AMCC1998/Robo-de-Luta/01.ficheiros_3d/Botzilla_braco_servo.stl

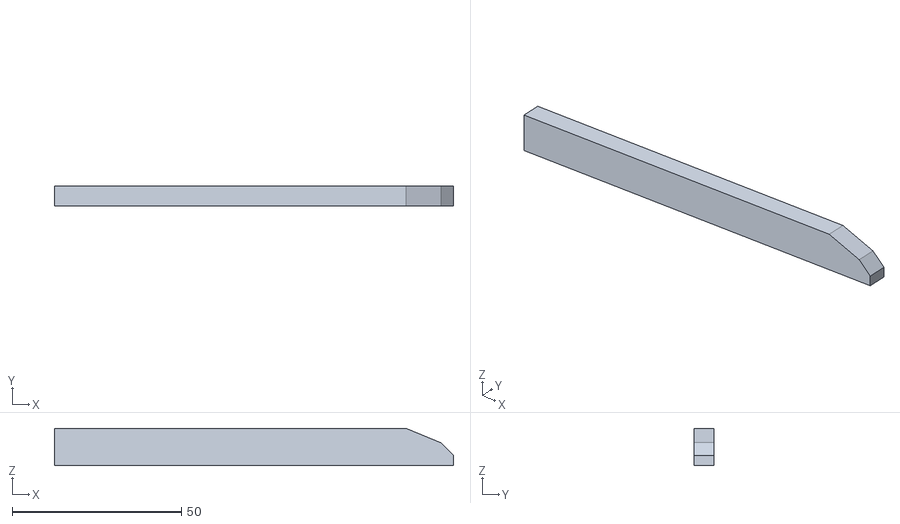
[picture p15: CAD file, 2025-08-01]
01.ficheiros_3d/Botzilla_braco_servo.stl
118.0 x 6.00 x 11.0
