AMCC1998/Robo-de-Luta/01.ficheiros_3d/v2/Botzilla_frame_esquerda.stl

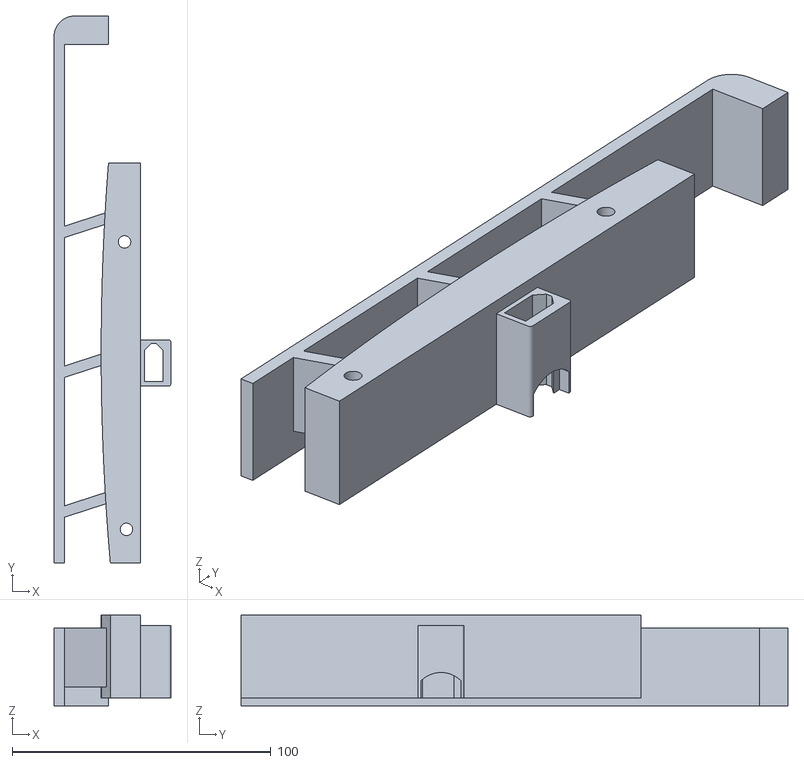
[picture p17: CAD file, 2025-10-28]
01.ficheiros_3d/v2/Botzilla_frame_esquerda.stl
45.2 x 211.2 x 35.0
