AMCC1998/Robo-de-Luta/01.ficheiros_3d/suporte_arma_esq.stl

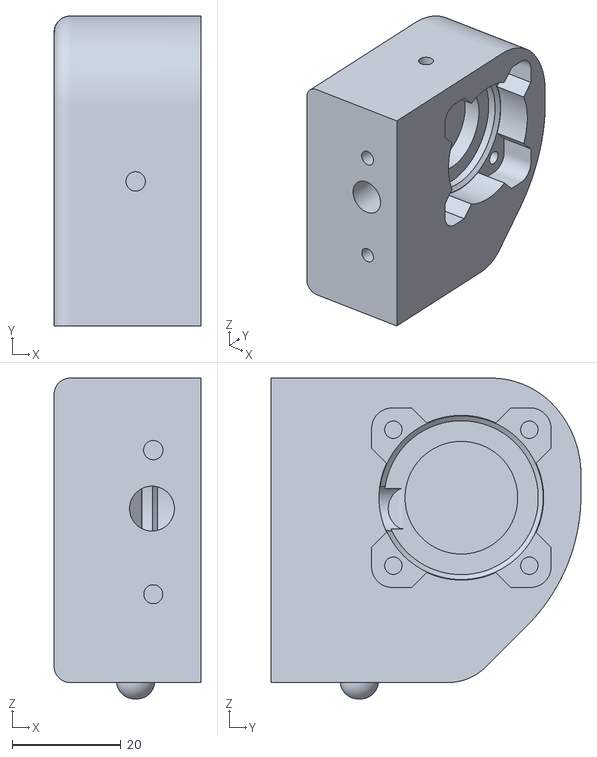
[picture p18: CAD file, 2025-08-01]
01.ficheiros_3d/suporte_arma_esq.stl
27.0 x 57.0 x 59.0
