AMCC1998/Robo-de-Luta/01.ficheiros_3d/v2/Suporte_fuzivel_2.stl

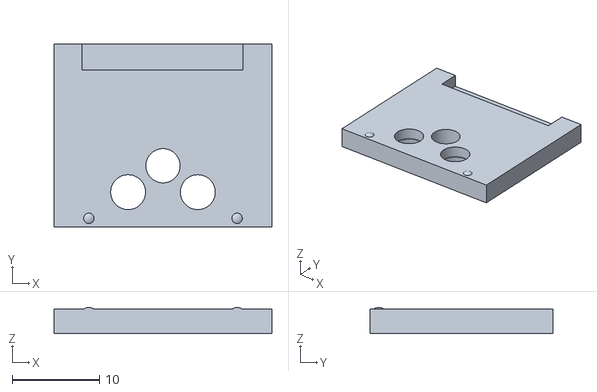
[picture p19: CAD file, 2025-10-28]
01.ficheiros_3d/v2/Suporte_fuzivel_2.stl
25.0 x 21.0 x 3.00
