AMCC1998/Robo-de-Luta/01.ficheiros_3d/body_tras.stl

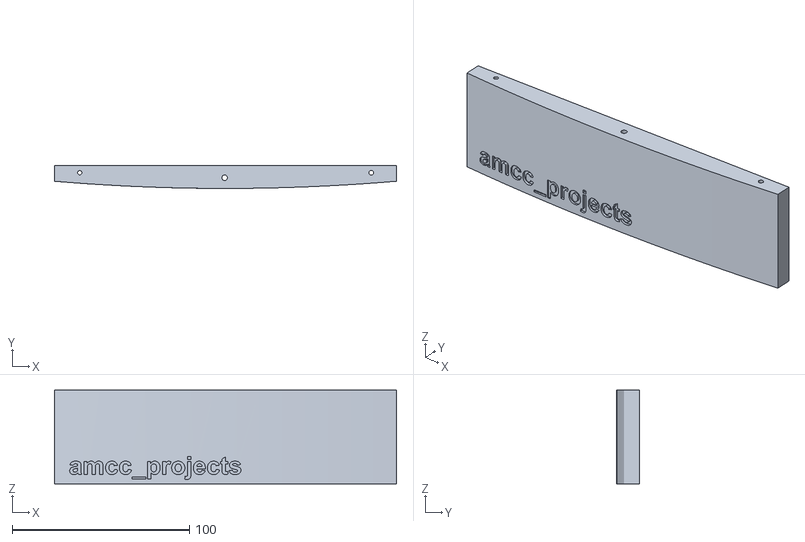
[picture p20: CAD file, 2025-08-01]
01.ficheiros_3d/body_tras.stl
193.0 x 12.9 x 53.0
