AMCC1998/Robo-de-Luta/01.ficheiros_3d/v2/Arma_4.stl

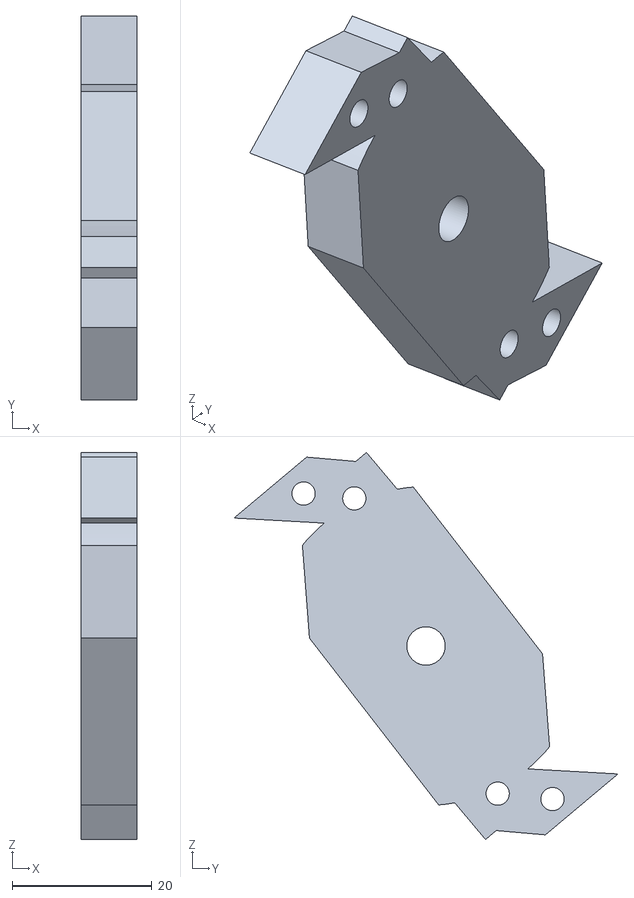
[picture p21: CAD file, 2025-10-28]
01.ficheiros_3d/v2/Arma_4.stl
8.00 x 55.0 x 55.5
