AMCC1998/Robo-de-Luta/01.ficheiros_3d/Tampa_superior_1mm.stl

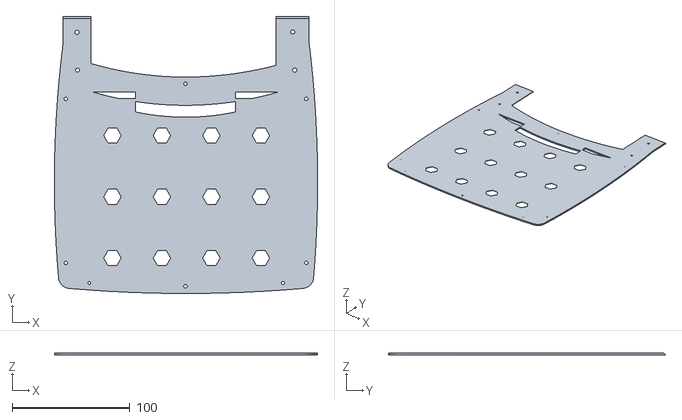
[picture p22: CAD file, 2025-08-01]
01.ficheiros_3d/Tampa_superior_1mm.stl
223.4 x 235.1 x 1.50
