AMCC1998/Robo-de-Luta/01.ficheiros_3d/Botzilla_lateral_esq.stl

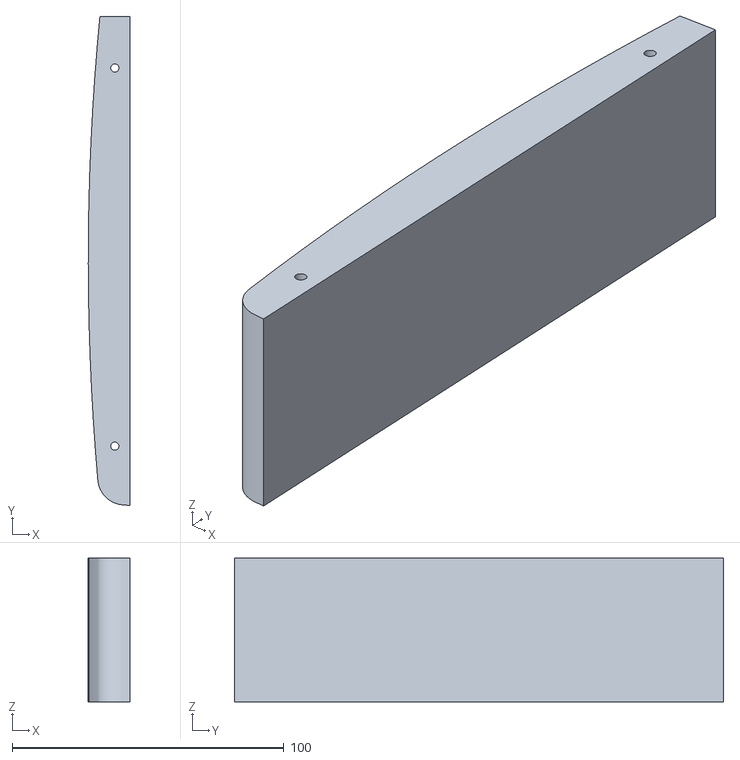
[picture p23: CAD file, 2025-08-01]
01.ficheiros_3d/Botzilla_lateral_esq.stl
15.3 x 180.0 x 53.0
