AMCC1998/Robo-de-Luta/01.ficheiros_3d/v2/Botzilla_frame_tras.stl

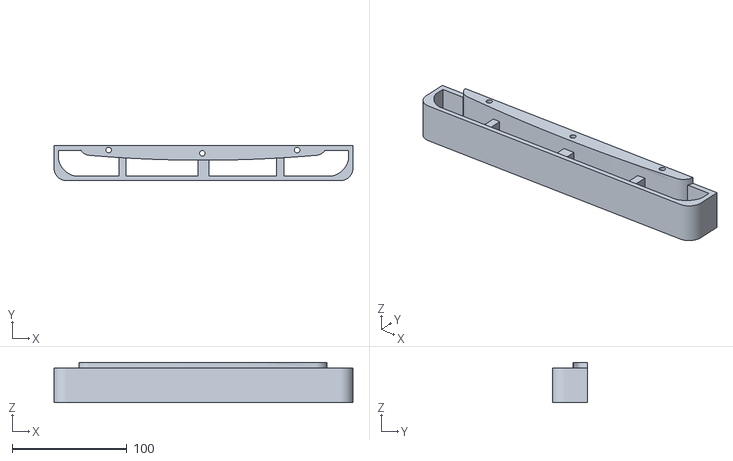
[picture p24: CAD file, 2025-10-28]
01.ficheiros_3d/v2/Botzilla_frame_tras.stl
261.0 x 30.8 x 35.0
