AMCC1998/Robo-de-Luta/01.ficheiros_3d/v2/Roda.stl

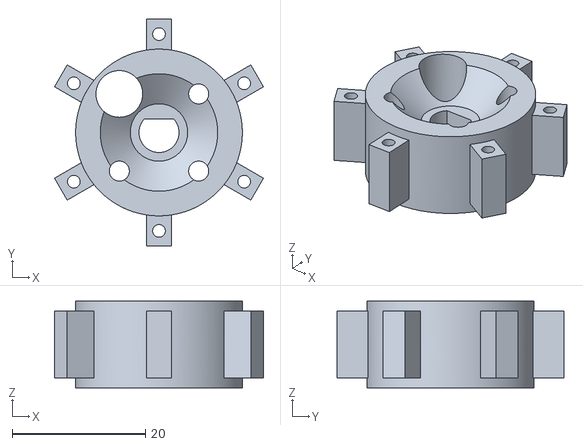
[picture p26: CAD file, 2025-10-28]
01.ficheiros_3d/v2/Roda.stl
31.3 x 34.0 x 13.0
