AMCC1998/Robo-de-Luta/01.ficheiros_3d/cabo_ferramenta_bloqueio.stl

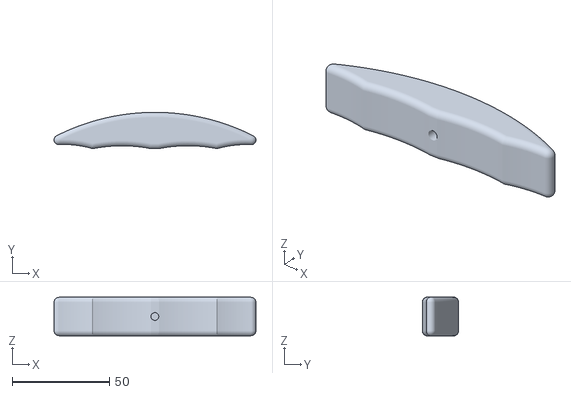
[picture p27: CAD file, 2025-08-01]
01.ficheiros_3d/cabo_ferramenta_bloqueio.stl
103.9 x 18.7 x 20.0
