AMCC1998/Robo-de-Luta/01.ficheiros_3d/v2/Arma.step

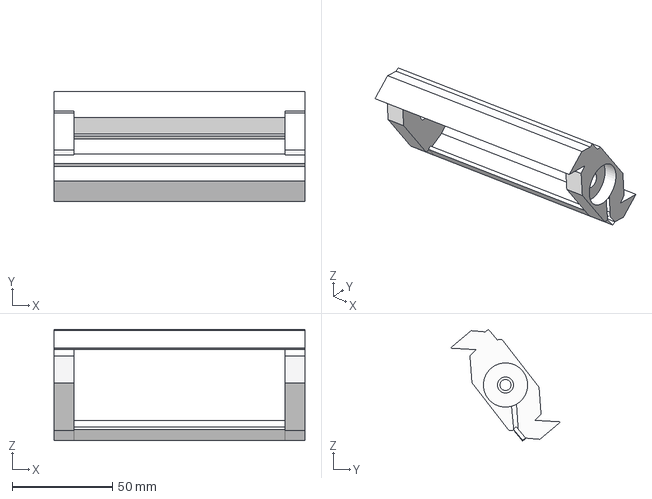
[picture p28: CAD file, 2025-10-28]
01.ficheiros_3d/v2/Arma.step
125.0 x 55.0 x 55.5 mm
