AMCC1998/Robo-de-Luta/01.ficheiros_3d/v2/Arma_dir.stl

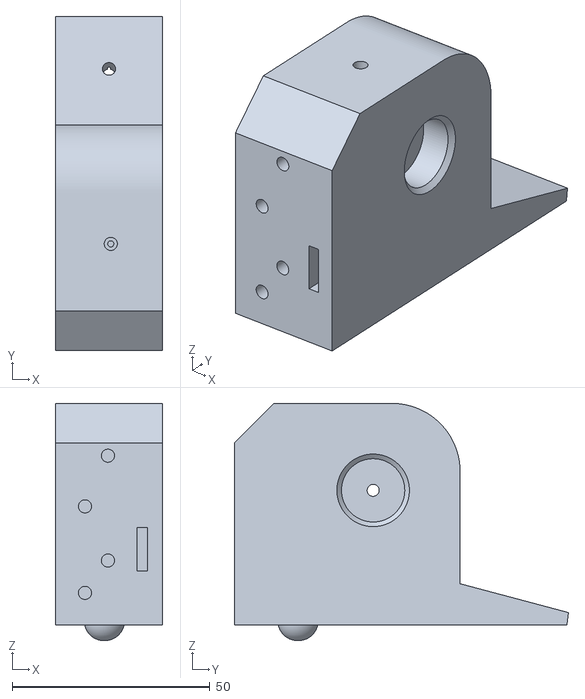
[picture p29: CAD file, 2025-10-28]
01.ficheiros_3d/v2/Arma_dir.stl
27.1 x 84.5 x 60.0
