AMCC1998/Robo-de-Luta/01.ficheiros_3d/base_baixo.stl

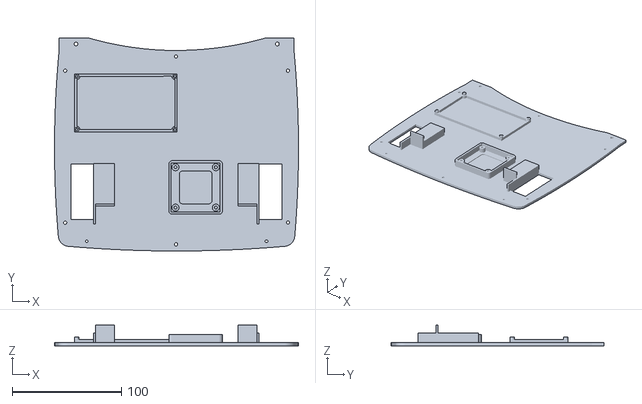
[picture p30: CAD file, 2025-08-01]
01.ficheiros_3d/base_baixo.stl
223.4 x 195.1 x 19.0
