AMCC1998/Robo-de-Luta/01.ficheiros_3d/v2/Molde_pneu.stl

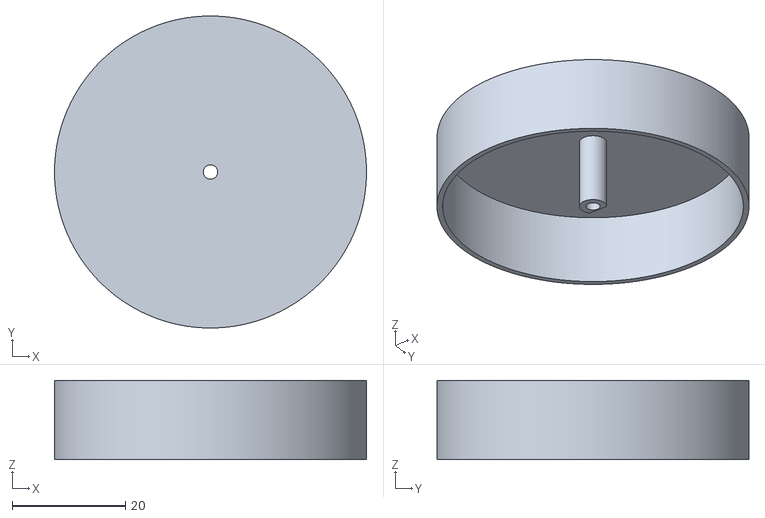
[picture p31: CAD file, 2025-10-28]
01.ficheiros_3d/v2/Molde_pneu.stl
55.0 x 55.0 x 14.0
