AMCC1998/Robo-de-Luta/01.ficheiros_3d/body_frente.stl

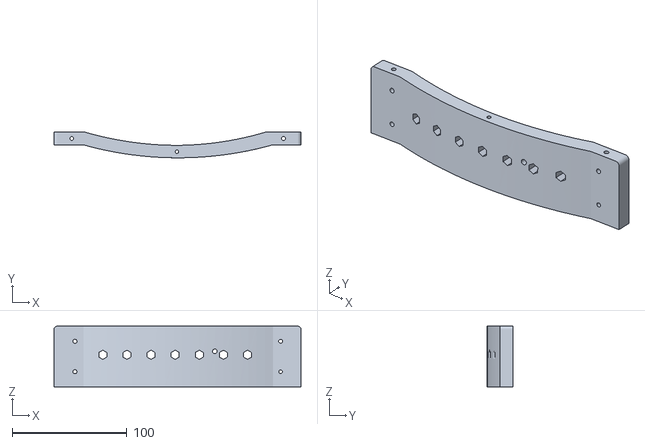
[picture p32: CAD file, 2025-08-01]
01.ficheiros_3d/body_frente.stl
215.0 x 22.3 x 53.0
