AMCC1998/Robo-de-Luta/01.ficheiros_3d/v2/Botzilla_frame_direita.stl

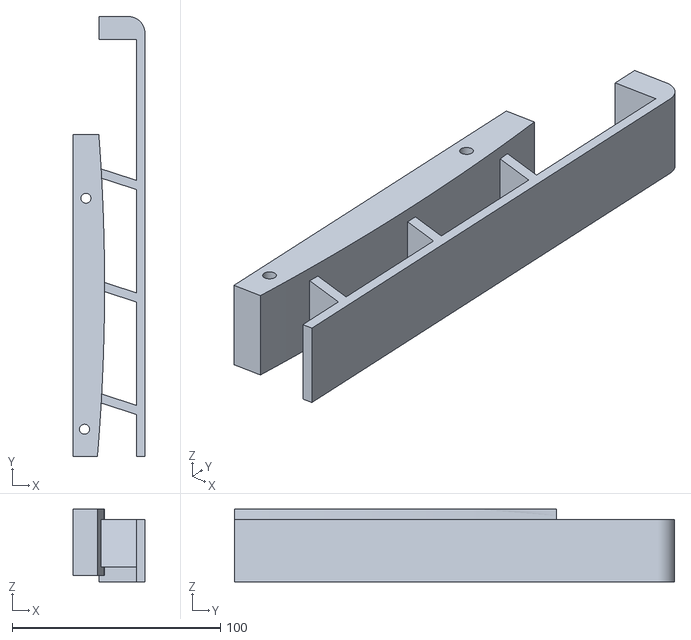
[picture p33: CAD file, 2025-10-28]
01.ficheiros_3d/v2/Botzilla_frame_direita.stl
34.5 x 211.2 x 35.0
