AMCC1998/Robo-de-Luta/01.ficheiros_3d/suporte_motor.stl

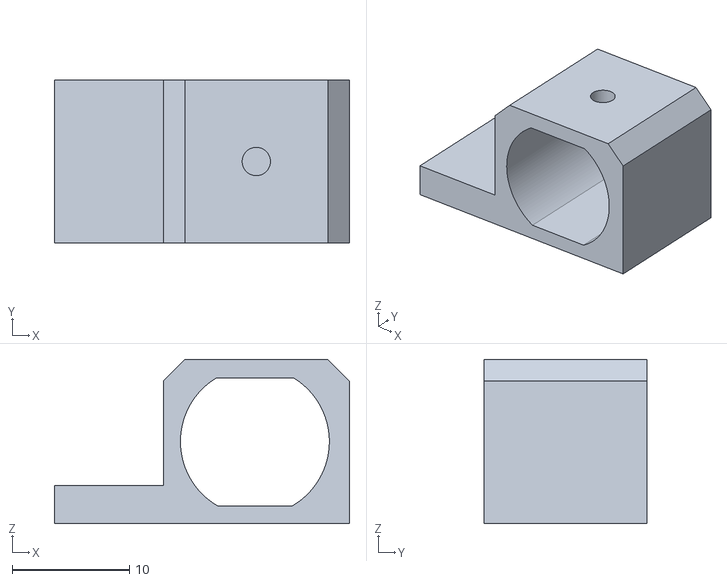
[picture p34: CAD file, 2025-06-23]
01.ficheiros_3d/suporte_motor.stl
25.1 x 13.9 x 14.0
