AMCC1998/Robo-de-Luta/01.ficheiros_3d/molde_pneu_roda.stl

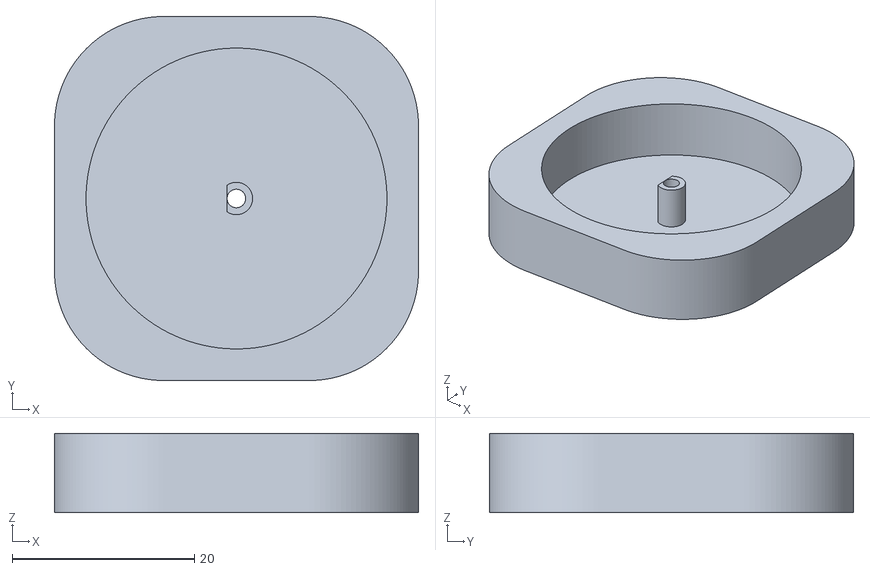
[picture p36: CAD file, 2025-06-23]
01.ficheiros_3d/molde_pneu_roda.stl
40.0 x 40.0 x 8.70
