AMCC1998/Robo-de-Luta/01.ficheiros_3d/v2/tampa_superior.stl

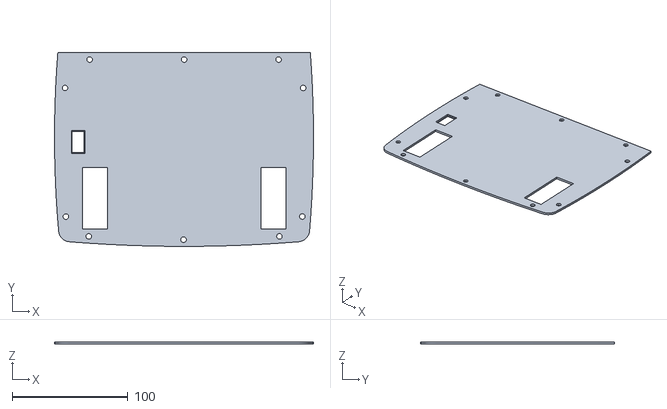
[picture p37: CAD file, 2025-10-28]
01.ficheiros_3d/v2/tampa_superior.stl
223.4 x 167.2 x 2.00
