AMCC1998/Robo-de-Luta/01.ficheiros_3d/molde_roda_Rodas.stl

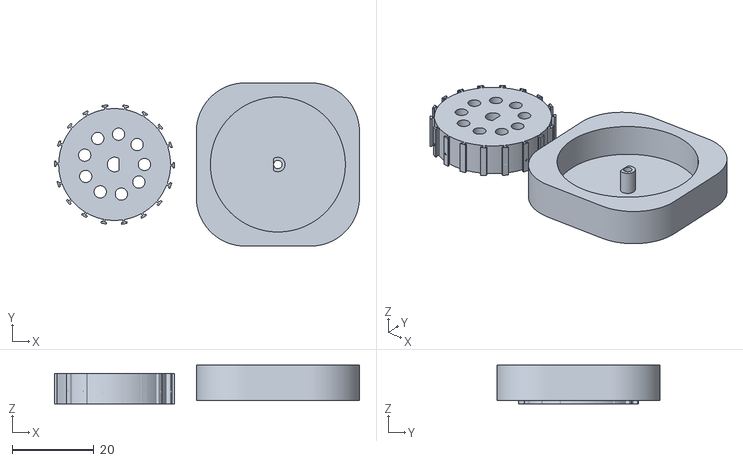
[picture p38: CAD file, 2025-06-23]
01.ficheiros_3d/molde_roda_Rodas.stl
74.7 x 40.0 x 9.50
