AMCC1998/Robo-de-Luta/01.ficheiros_3d/roda.stl

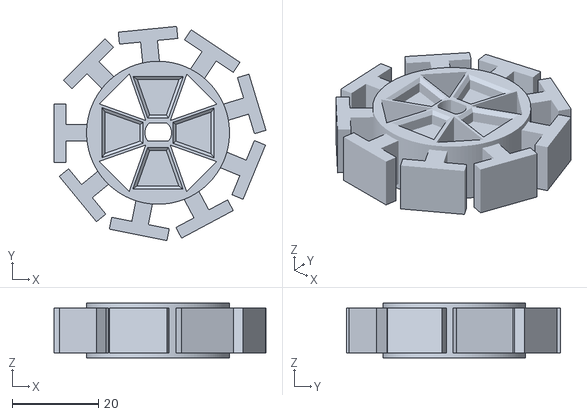
[picture p39: CAD file, 2025-06-23]
01.ficheiros_3d/roda.stl
49.2 x 49.7 x 12.7
