AMCC1998/Robo-de-Luta/01.ficheiros_3d/v2/Base_motor.stl

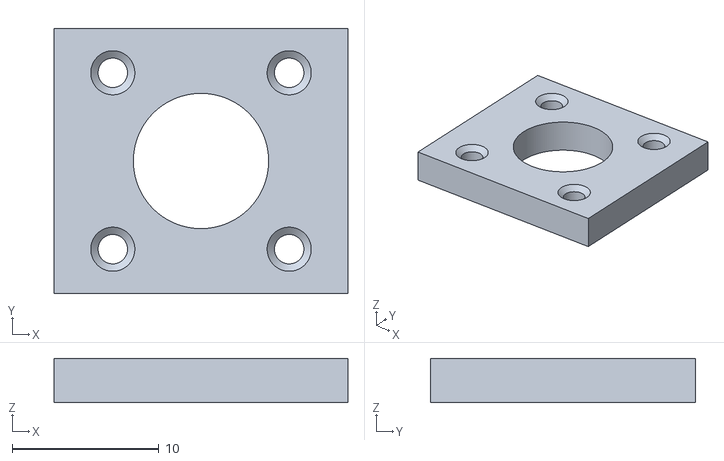
[picture p40: CAD file, 2025-09-01]
01.ficheiros_3d/v2/Base_motor.stl
20.0 x 18.0 x 3.00
