AMCC1998/Robo-de-Luta/01.ficheiros_3d/v2/Robo de luta v2.stl

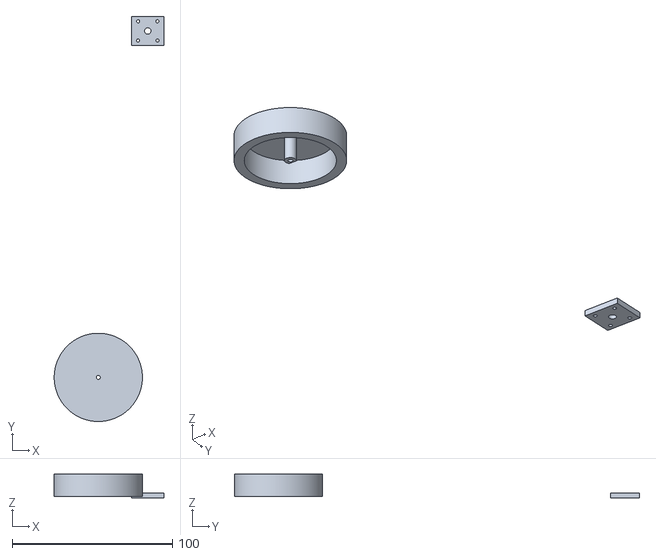
[picture p41: CAD file, 2025-09-01]
01.ficheiros_3d/v2/Robo de luta v2.stl
68.3 x 252.4 x 14.8
