AMCC1998/Robo-de-Luta/01.ficheiros_3d/v2/lateral_esq.stl

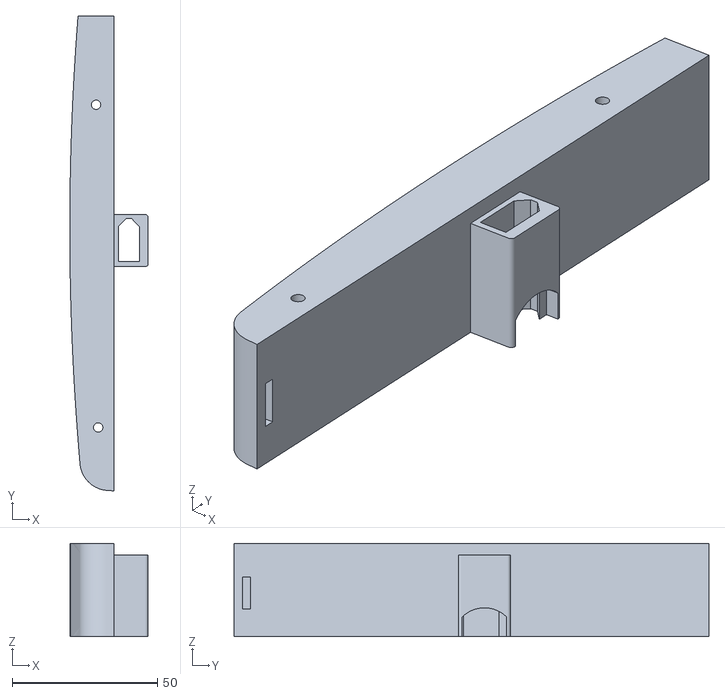
[picture p42: CAD file, 2025-09-01]
01.ficheiros_3d/v2/lateral_esq.stl
27.0 x 163.4 x 32.0
