AMCC1998/Robo-de-Luta/01.ficheiros_3d/v2/Body 51.stl

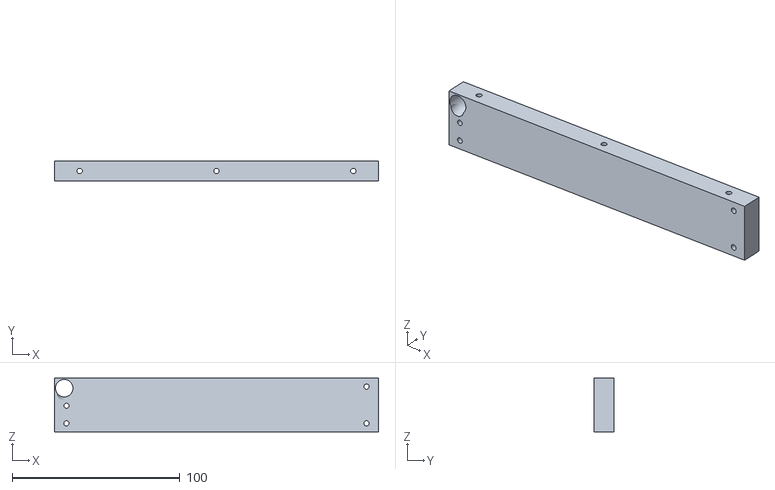
[picture p43: CAD file, 2025-09-01]
01.ficheiros_3d/v2/Body 51.stl
193.0 x 12.0 x 32.0
