AMCC1998/Robo-de-Luta/01.ficheiros_3d/v2/Botzilla.3mf

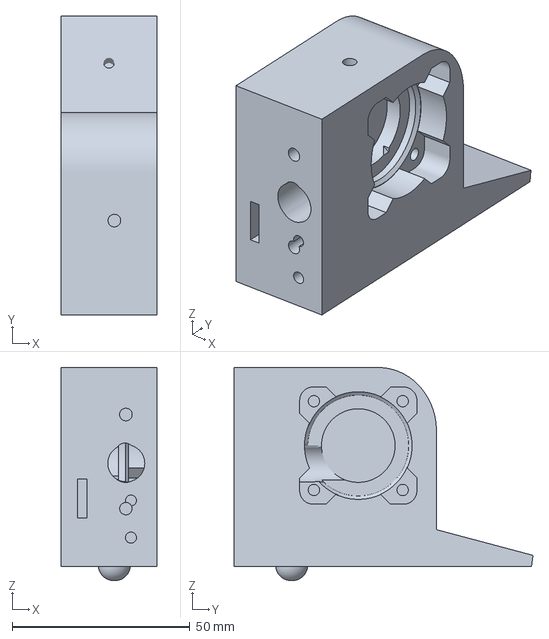
[picture p44: CAD file, 2025-09-01]
01.ficheiros_3d/v2/Botzilla.3mf
27.0 x 84.2 x 60.0 mm
