AMCC1998/Robo-de-Luta/01.ficheiros_3d/v2/Robo de luta v12.step

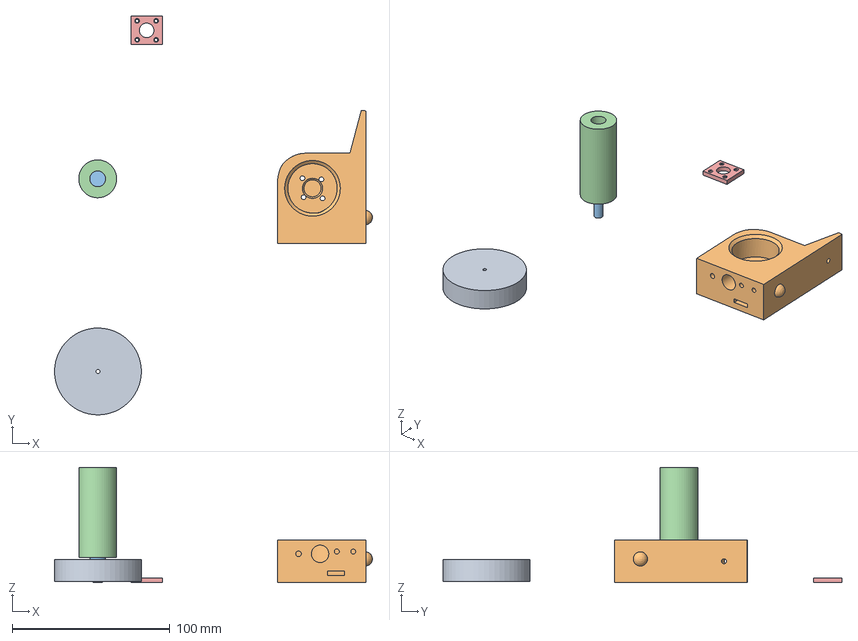
[picture p45: CAD file, 2025-09-01]
01.ficheiros_3d/v2/Robo de luta v12.step
201.3 x 252.4 x 73.0 mm
Molde_pneu
suporte arma esq
