AMCC1998/Robo-de-Luta/01.ficheiros_3d/v2/Body1.stl

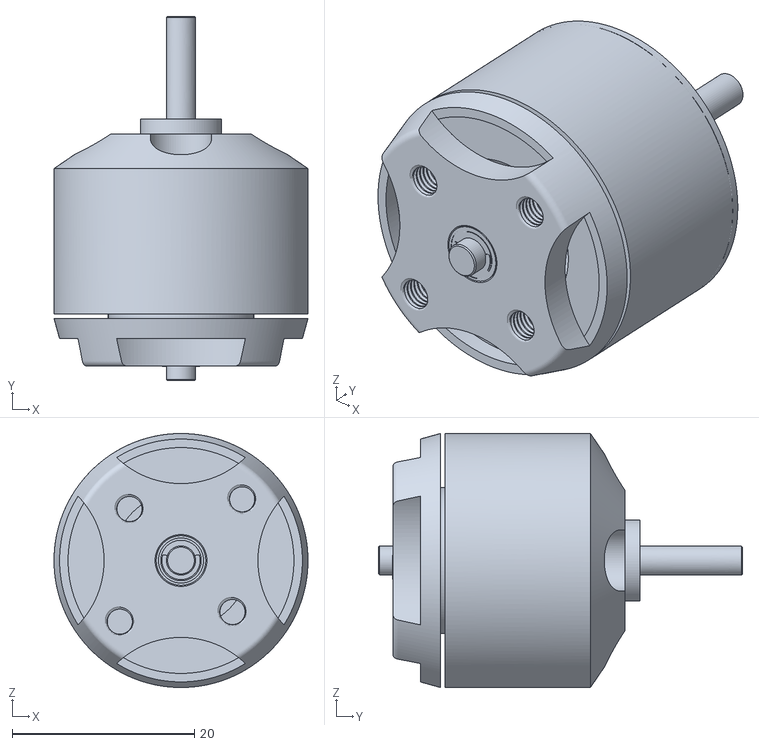
[picture p46: CAD file, 2025-09-01]
01.ficheiros_3d/v2/Body1.stl
27.9 x 40.0 x 27.9
