AMCC1998/Robo-de-Luta/01.ficheiros_3d/v2/Botzilla_lateral_traseira.stl

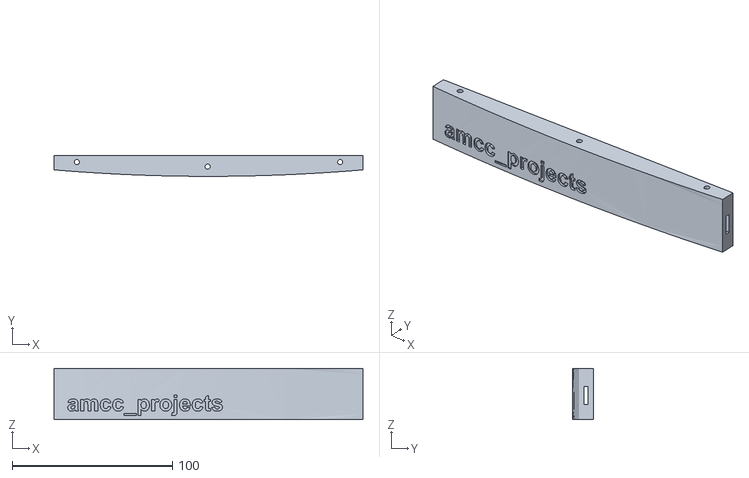
[picture p47: CAD file, 2025-09-01]
01.ficheiros_3d/v2/Botzilla_lateral_traseira.stl
193.0 x 12.9 x 32.0
