AMCC1998/Robo-de-Luta/01.ficheiros_3d/v2/suporte arma esq.step

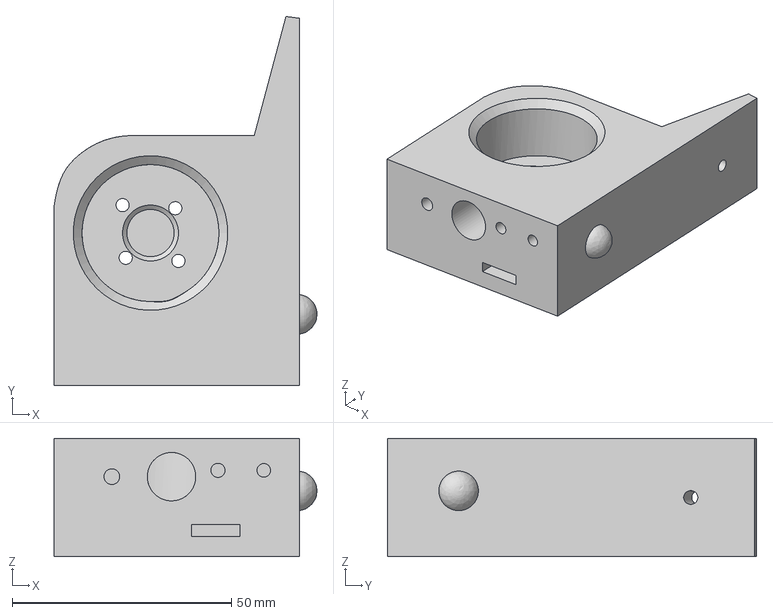
[picture p48: CAD file, 2025-09-01]
01.ficheiros_3d/v2/suporte arma esq.step
60.0 x 84.2 x 27.0 mm
