AMCC1998/Robo-de-Luta/01.ficheiros_3d/v2/lateral_dir.stl

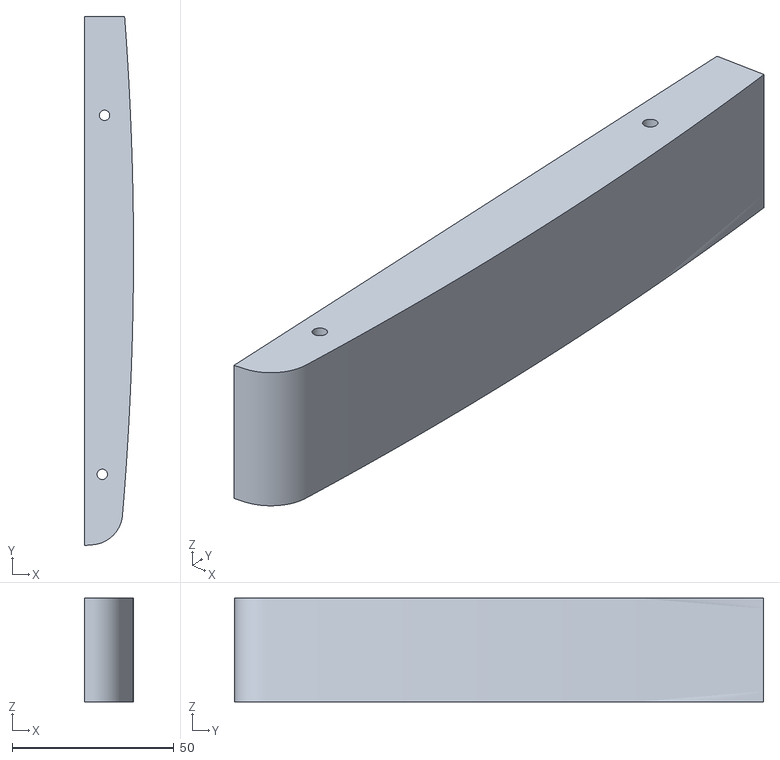
[picture p49: CAD file, 2025-09-01]
01.ficheiros_3d/v2/lateral_dir.stl
15.1 x 163.4 x 32.0
